Nauman3S/SmartMotorsMonitor/Circuit/Circuit_bb.png

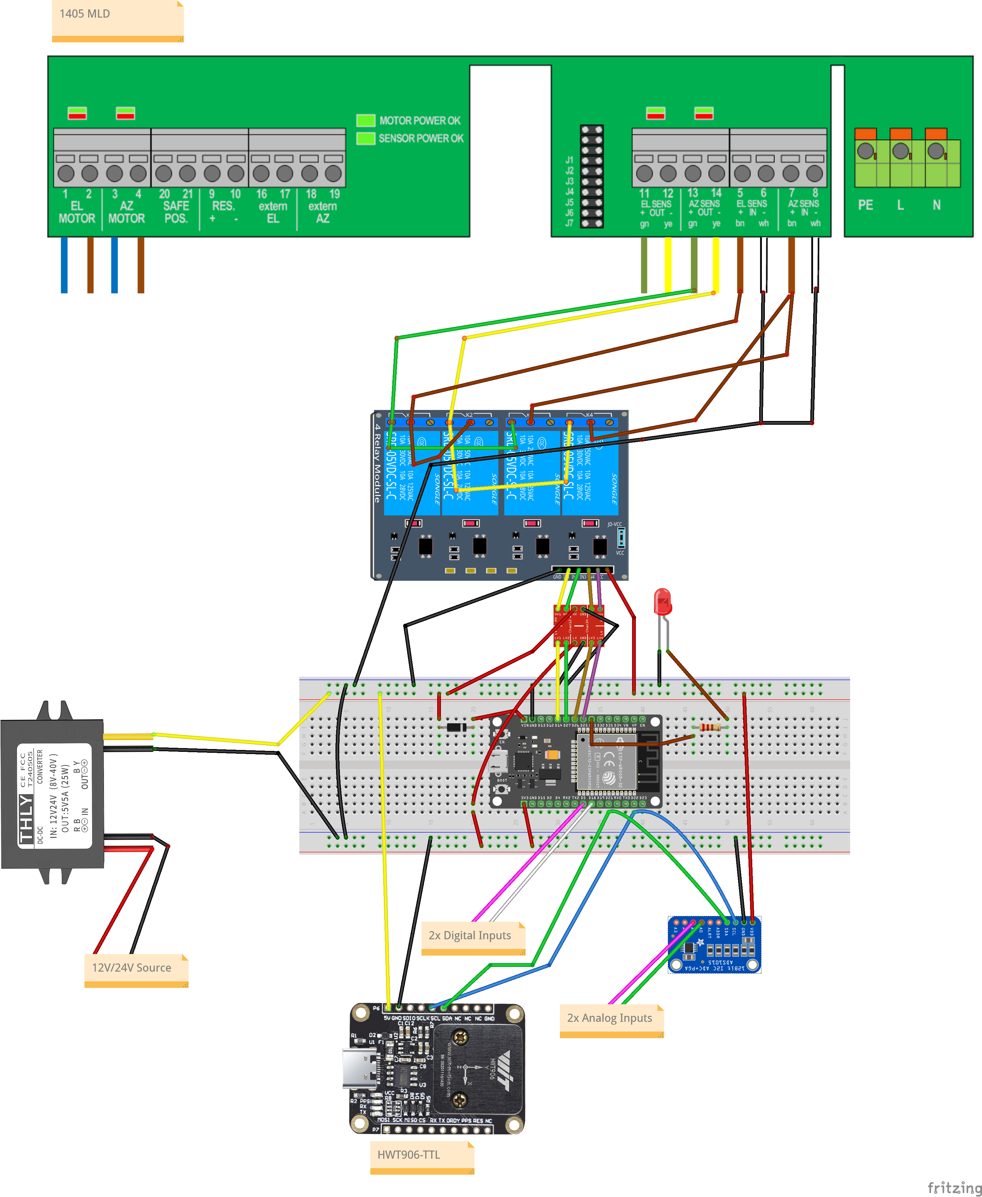
Circuit/Circuit_bb.png
