Nauman3S/SmartMotorsMonitor/Circuit/hwt.png

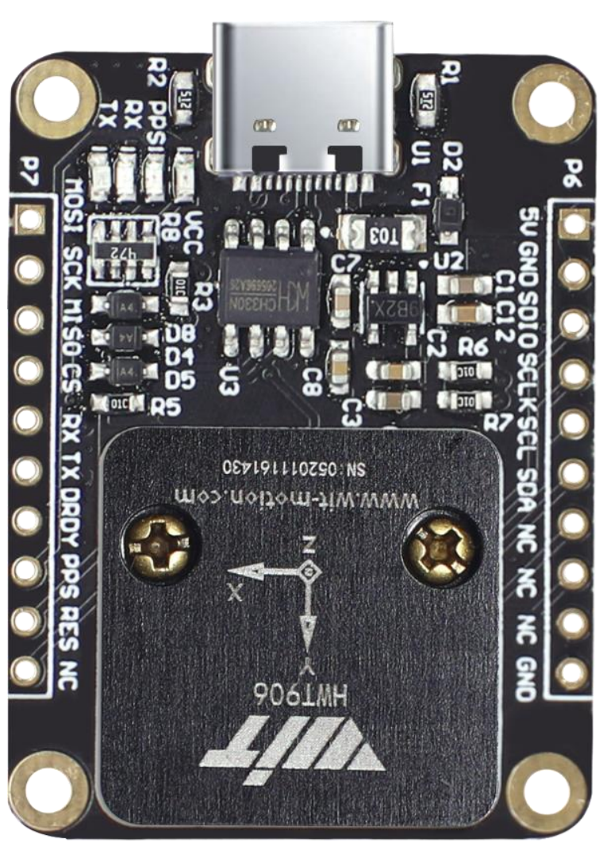
Circuit/hwt.png
