Nauman3S/SmartMotorsMonitor/Circuit/mldControl.png

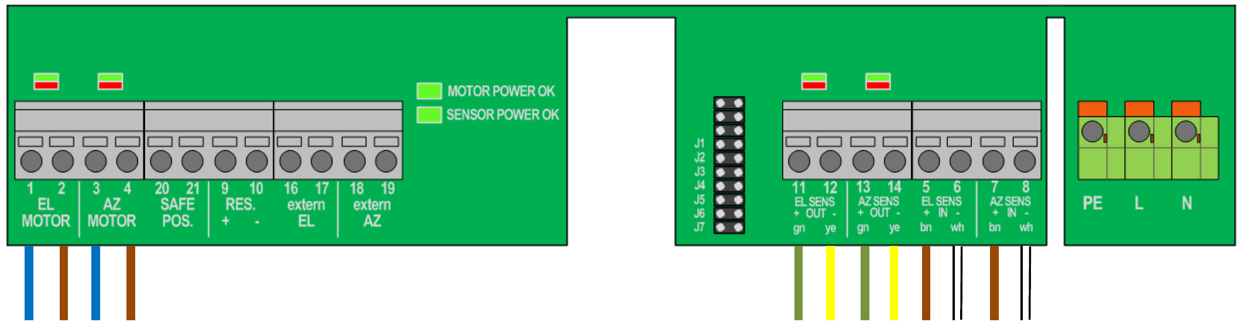
Circuit/mldControl.png
